globel420/Project-1/Binary_Counter_Only/Flowcharts/Binary_Counter_LED_Loop.png

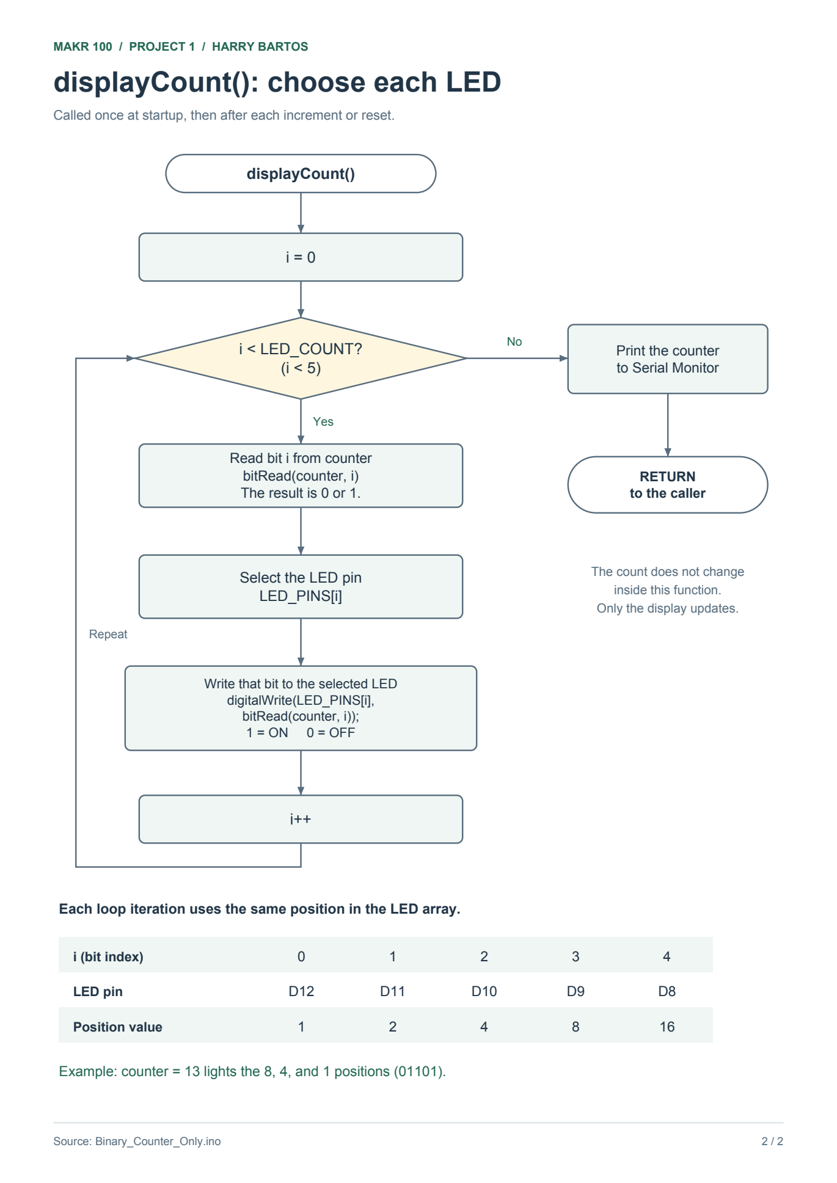
Binary_Counter_Only/Flowcharts/Binary_Counter_LED_Loop.png
