globel420/Project-1/Binary_Counter_Only/Flowcharts/Binary_Counter_Main_Flowchart.png

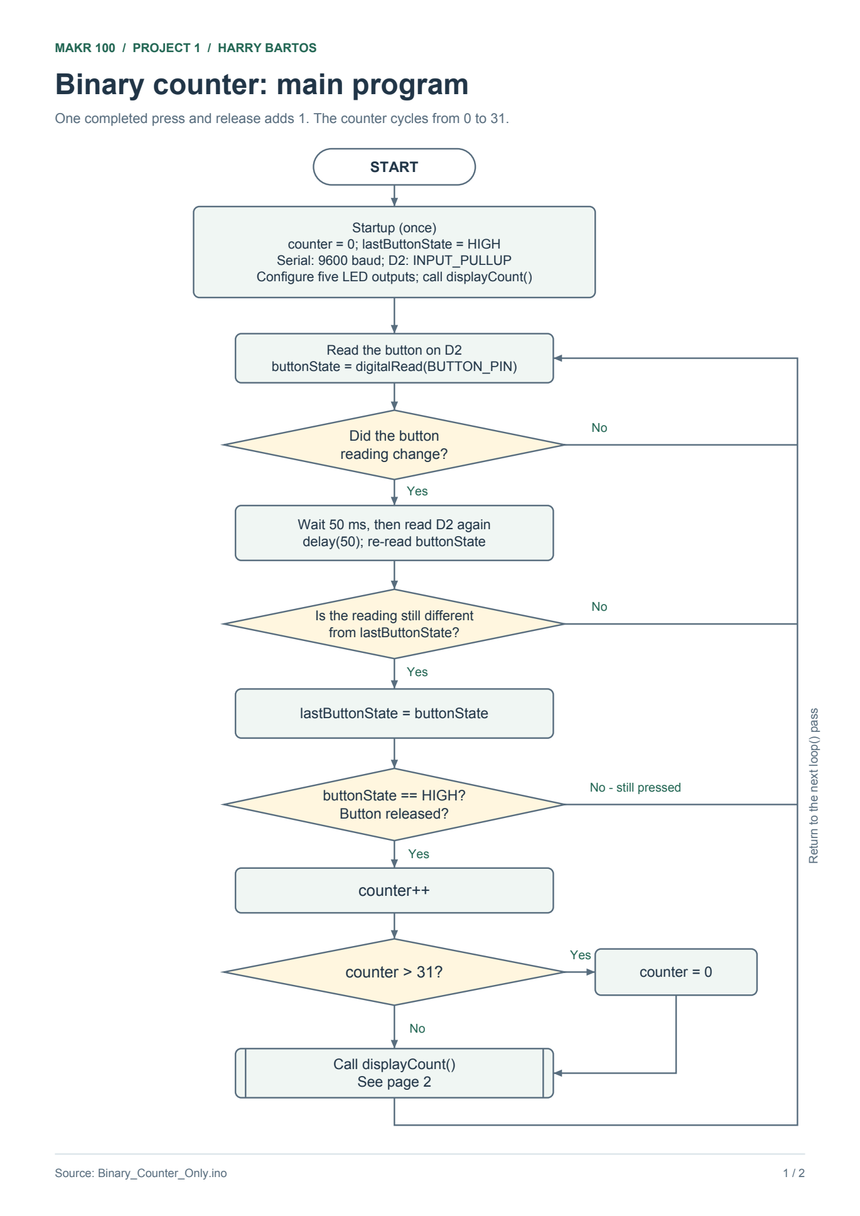
Binary_Counter_Only/Flowcharts/Binary_Counter_Main_Flowchart.png
