globel420/Project-1/Flowcharts/Program_Binary_Counter.png

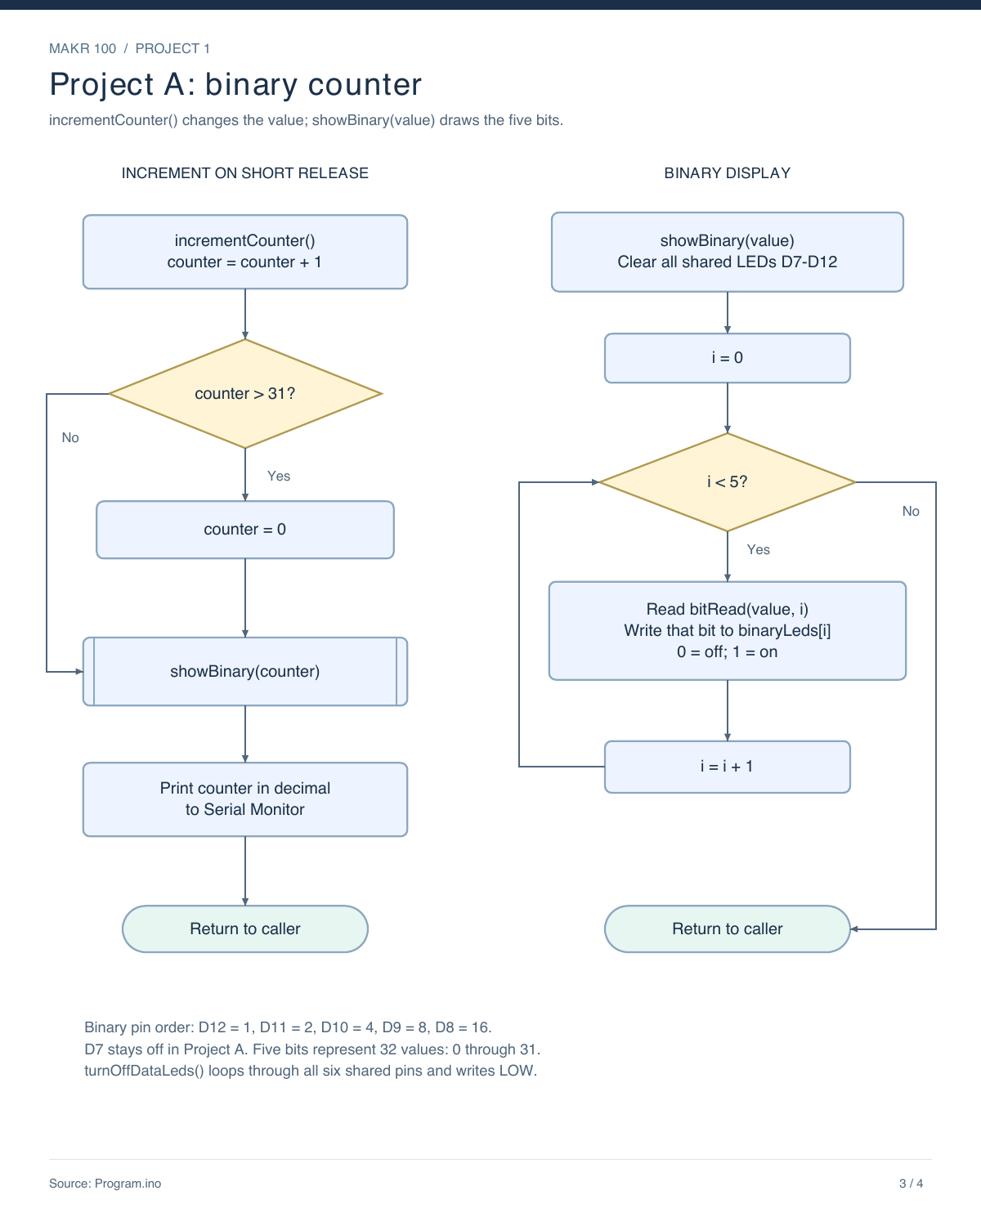
Flowcharts/Program_Binary_Counter.png
