globel420/Project-1/Flowcharts/Program_Logic_Operators.png

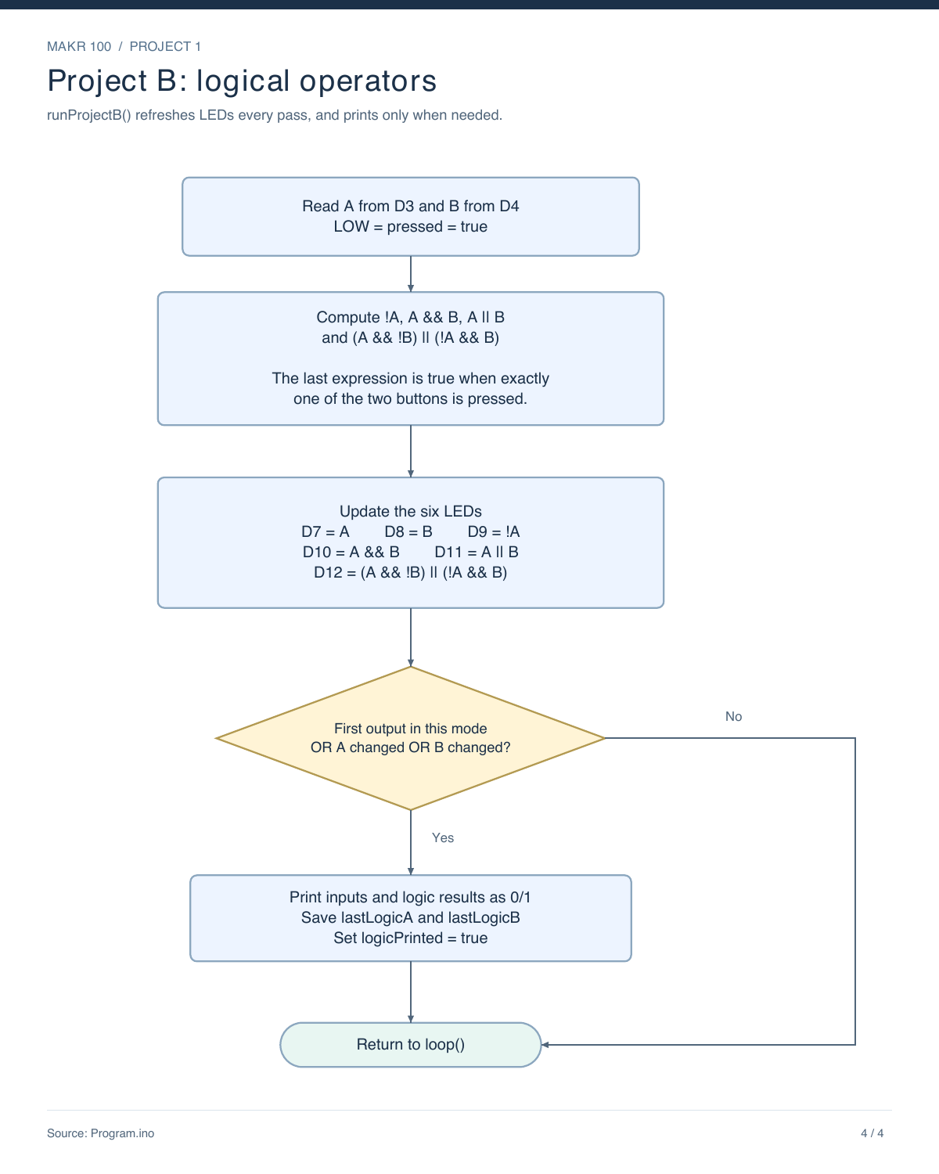
Flowcharts/Program_Logic_Operators.png
