globel420/Project-1/Flowcharts/Program_Main_Flowchart.png

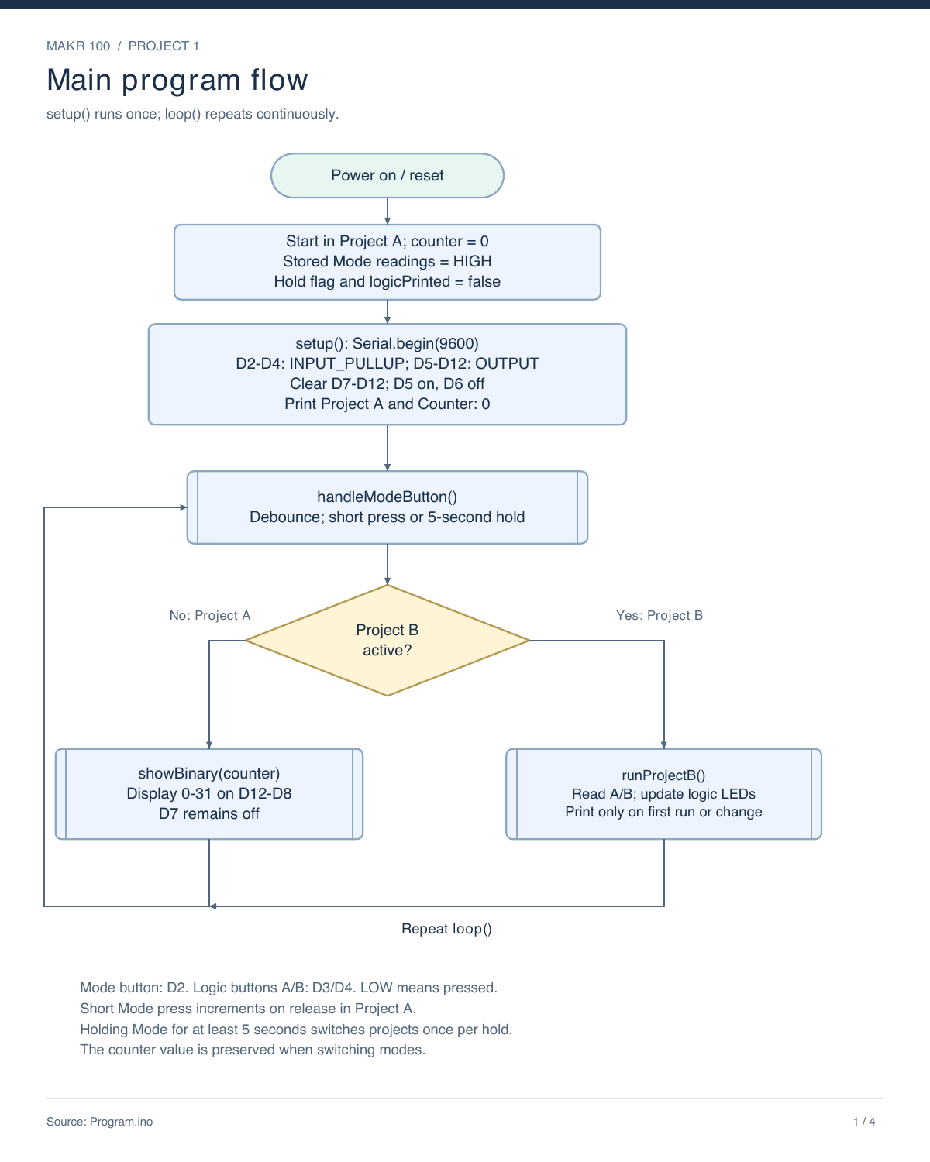
Flowcharts/Program_Main_Flowchart.png
