globel420/Project-1/Flowcharts/Program_Mode_Button.png

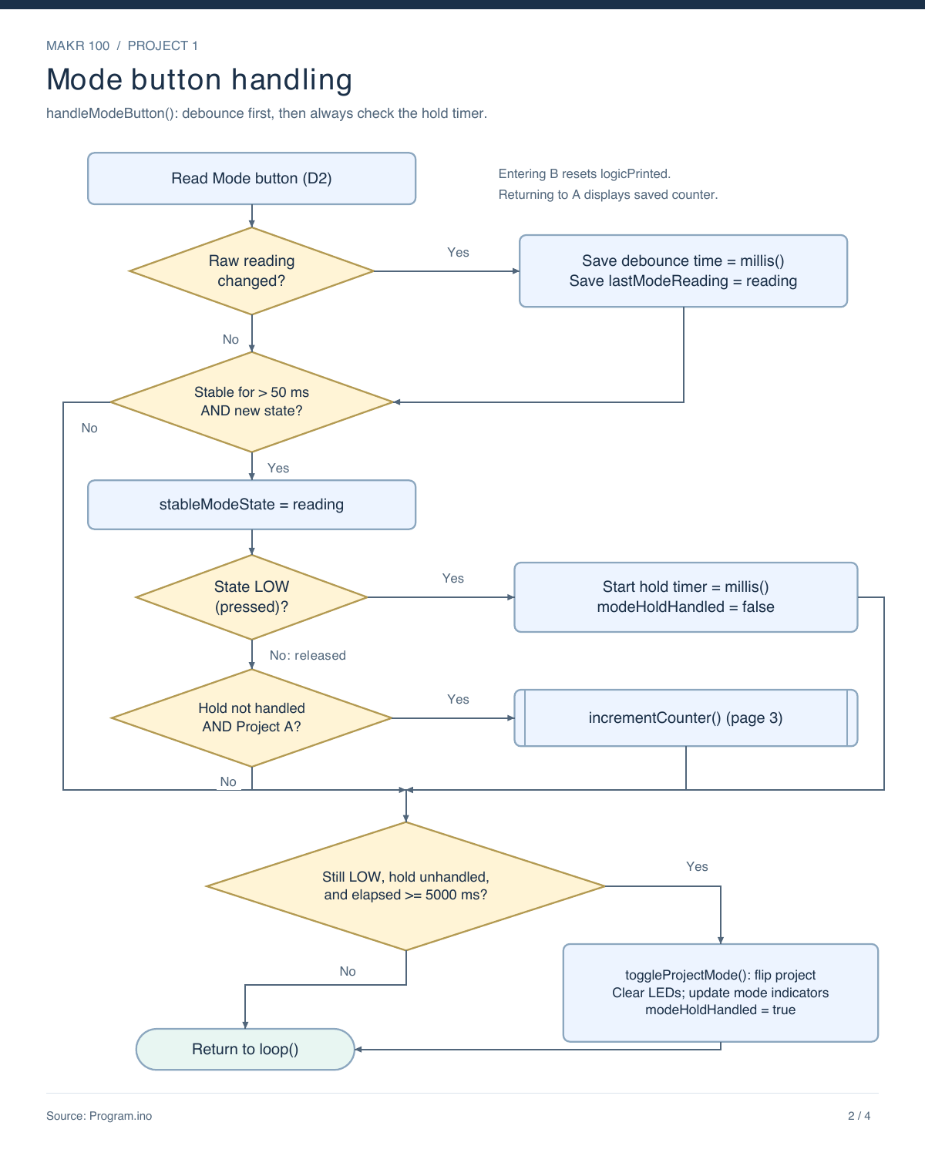
Flowcharts/Program_Mode_Button.png
