globel420/Project-1/Images/Flowchart_1_Master_Loop.png

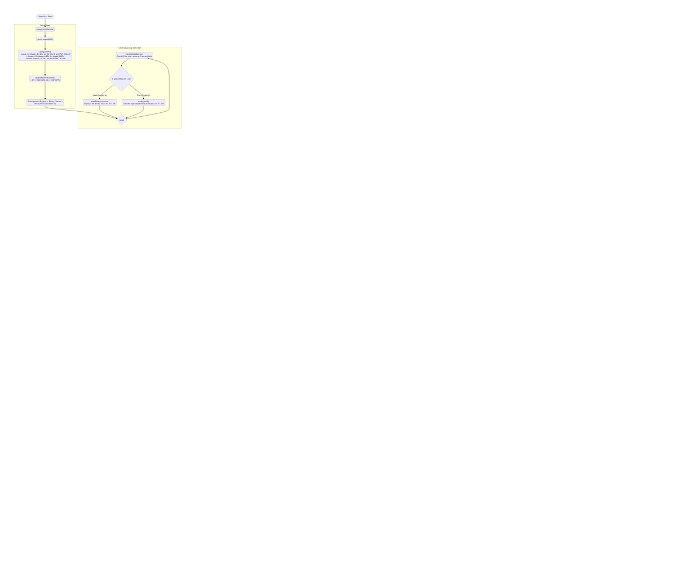
Images/Flowchart_1_Master_Loop.png
