globel420/Project-1/Images/Flowchart_2_Mode_Button.png

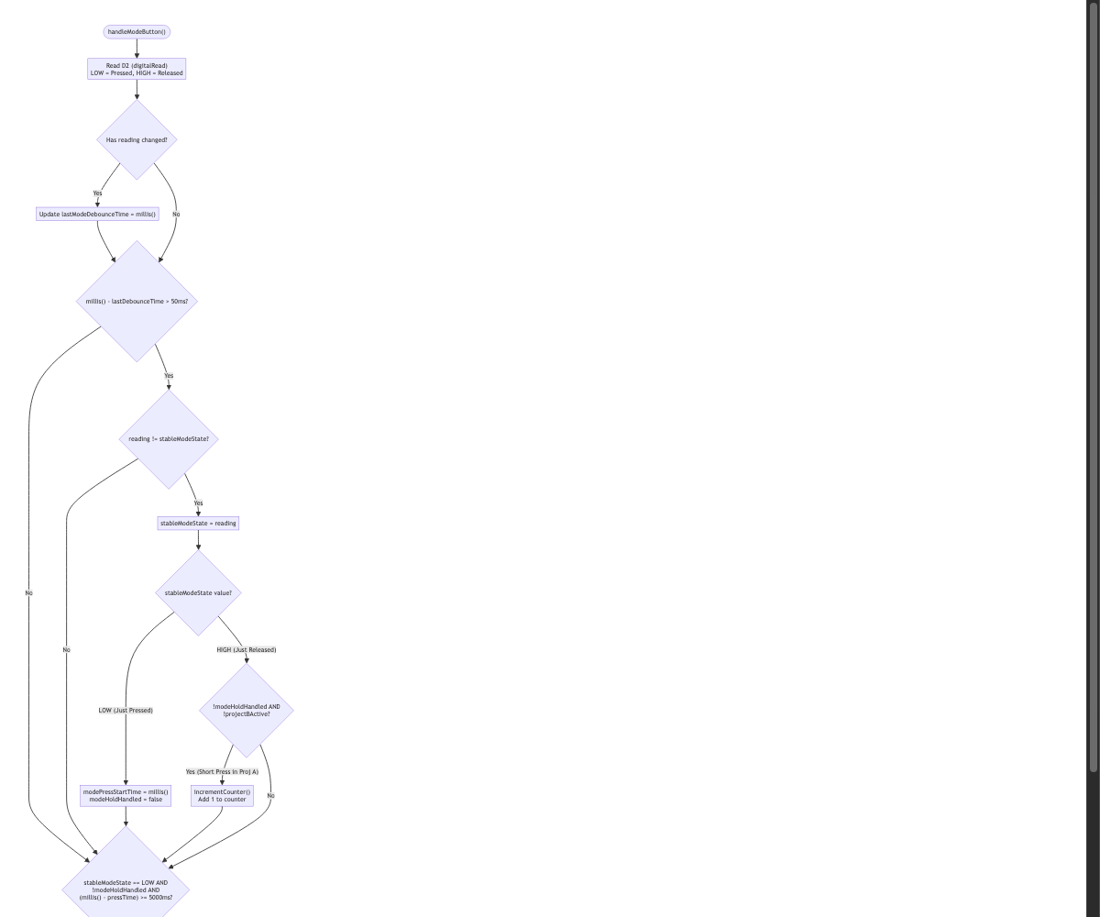
Images/Flowchart_2_Mode_Button.png
