globel420/Project-1/Images/Flowchart_4_Project_B_Logic.png

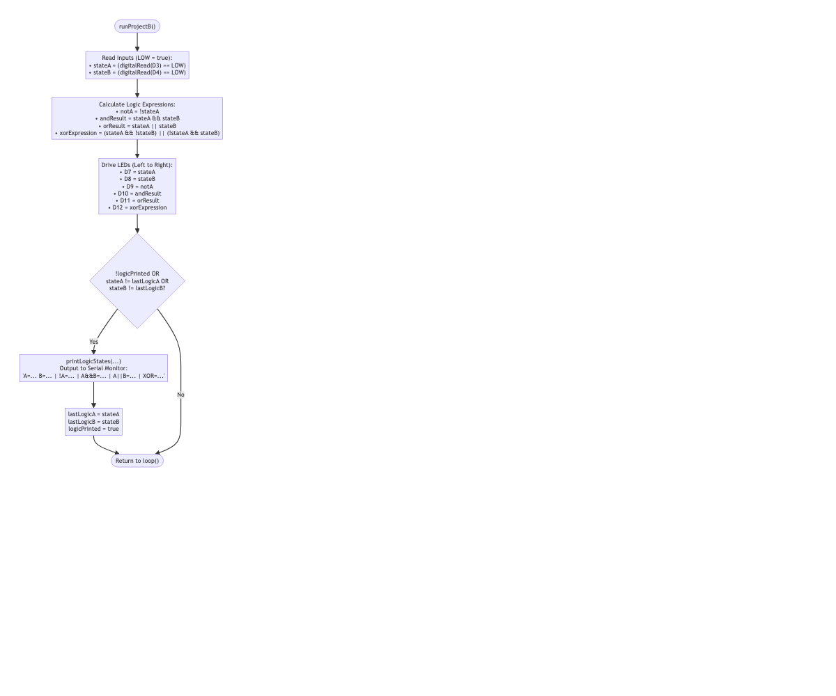
Images/Flowchart_4_Project_B_Logic.png
