globel420/Project-1/output/playwright/animation-binary-loop.png

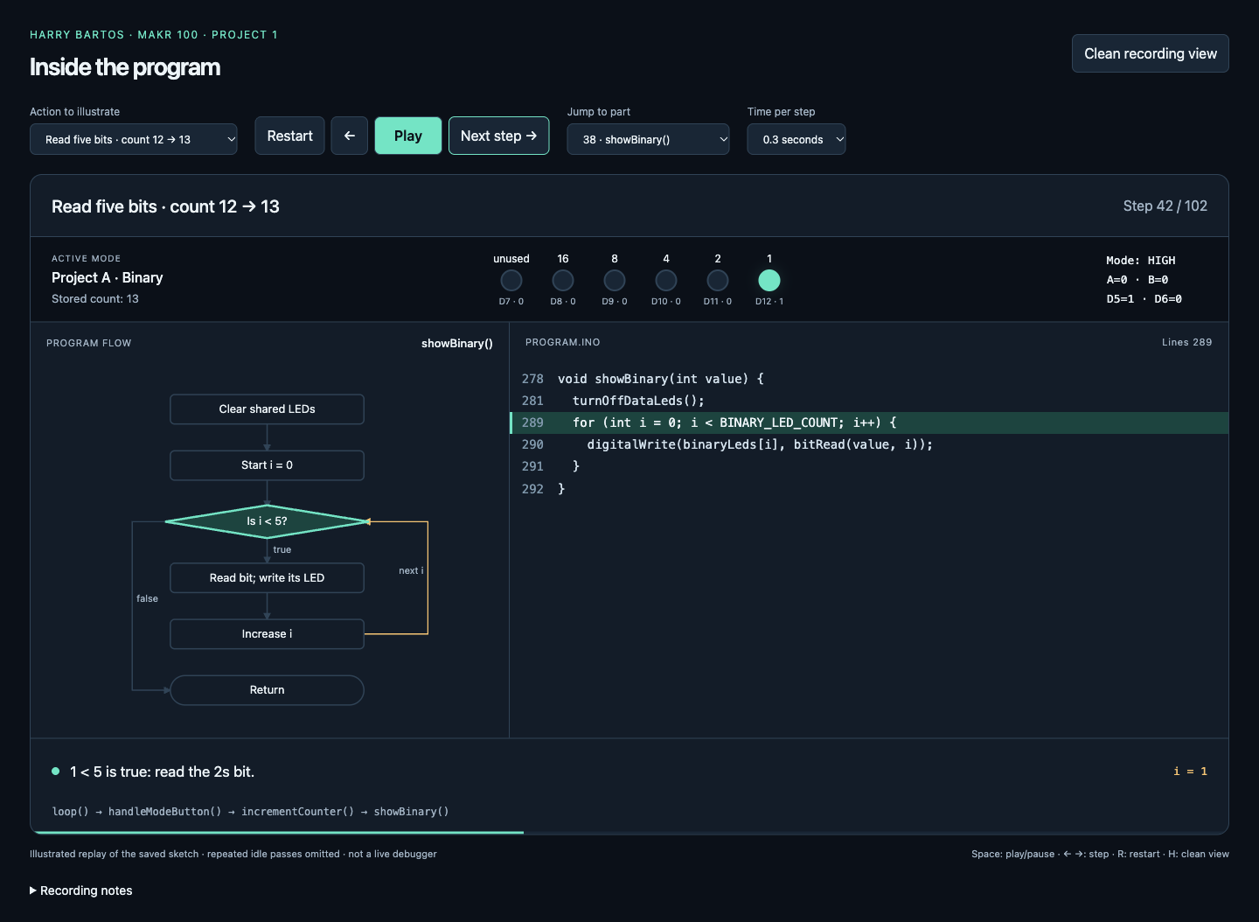
output/playwright/animation-binary-loop.png
