globel420/Project-1/output/playwright/animation-mobile.png

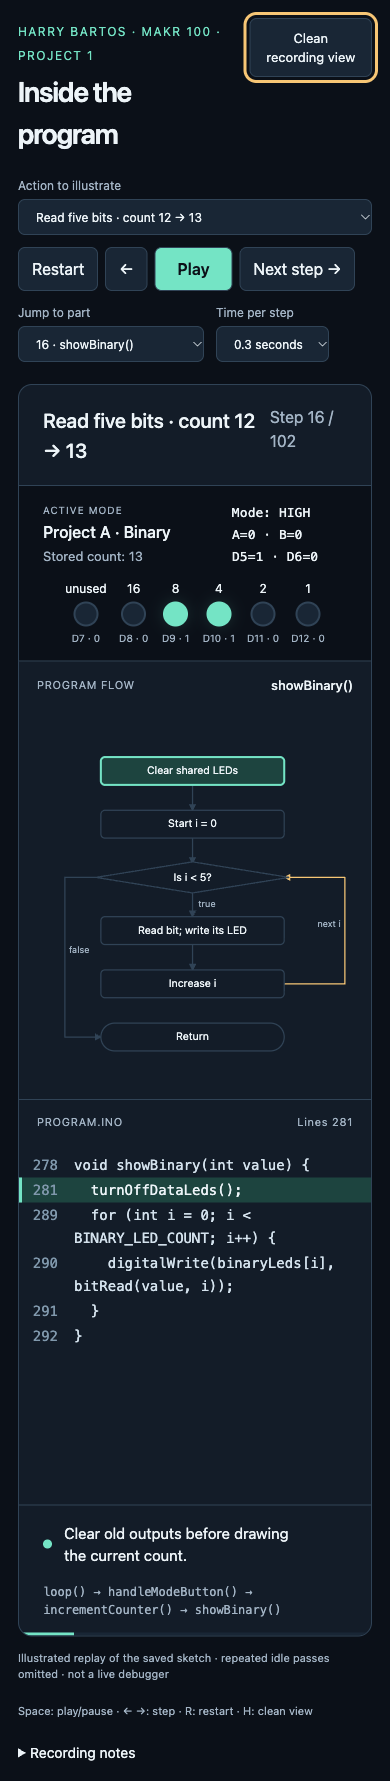
output/playwright/animation-mobile.png
