globel420/Project-1/Pictures/IMG_6296.jpeg

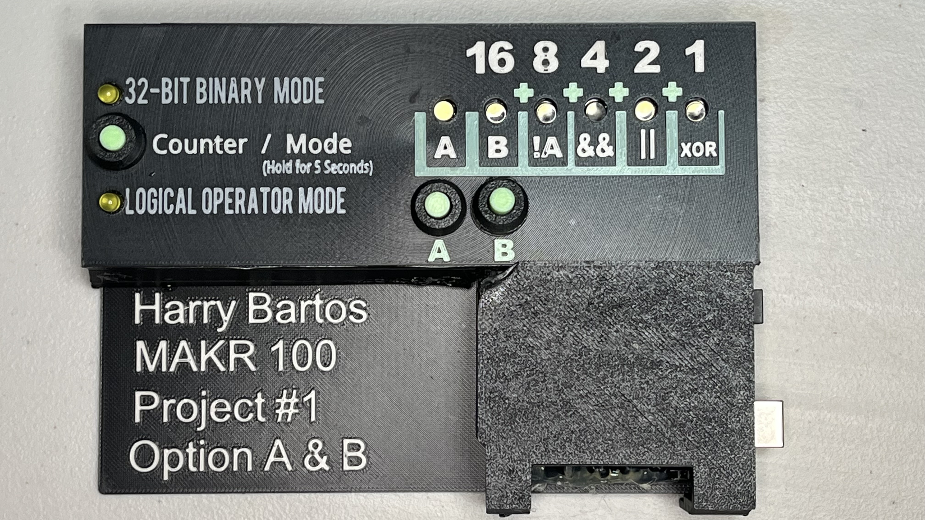
Pictures/IMG_6296.jpeg
