globel420/Project-1/Pictures/IMG_6298.jpeg

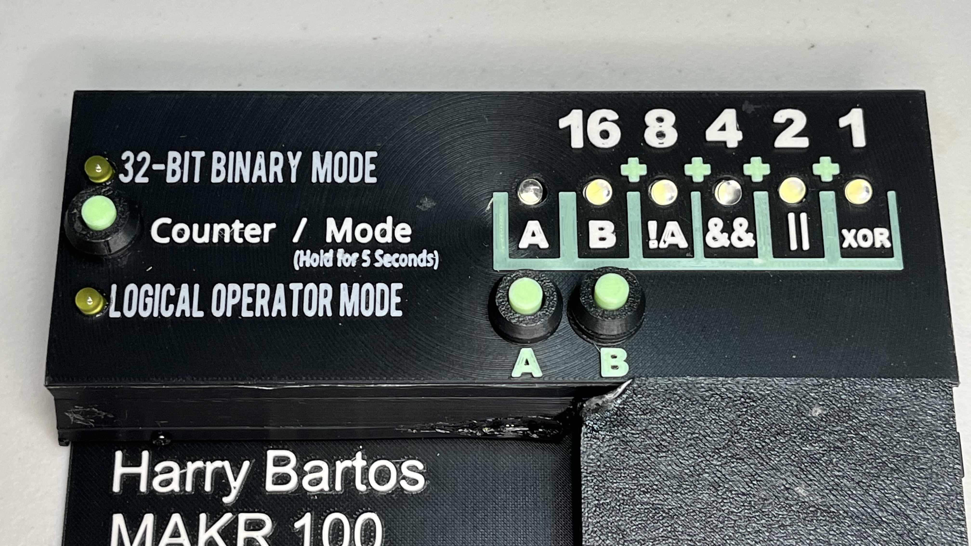
Pictures/IMG_6298.jpeg
