globel420/Project-1/Pictures/IMG_6299.jpeg

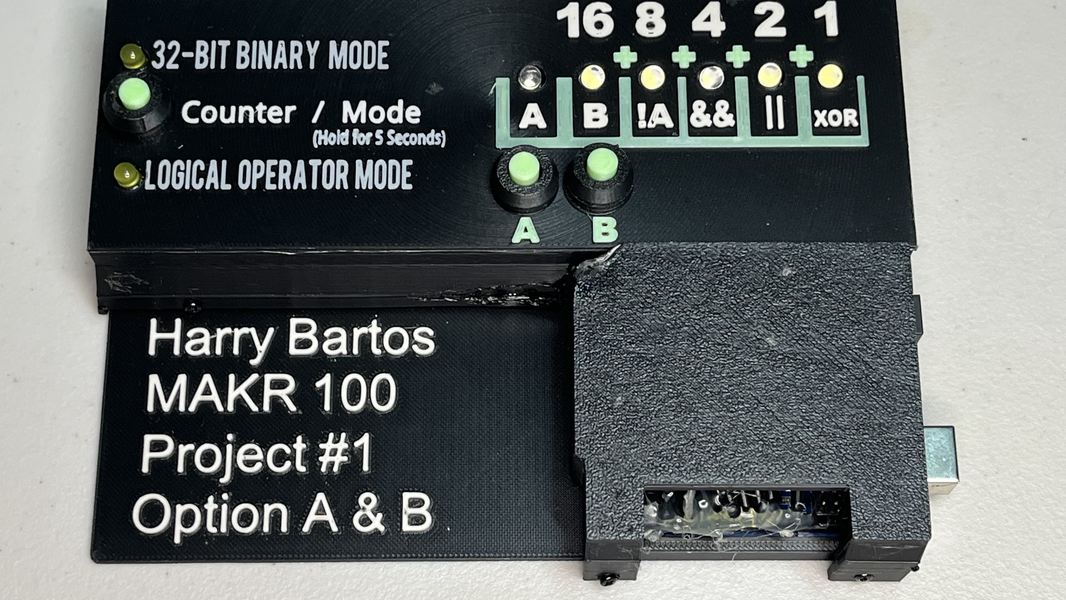
Pictures/IMG_6299.jpeg
