globel420/Project-1/Pictures/IMG_6301.jpeg

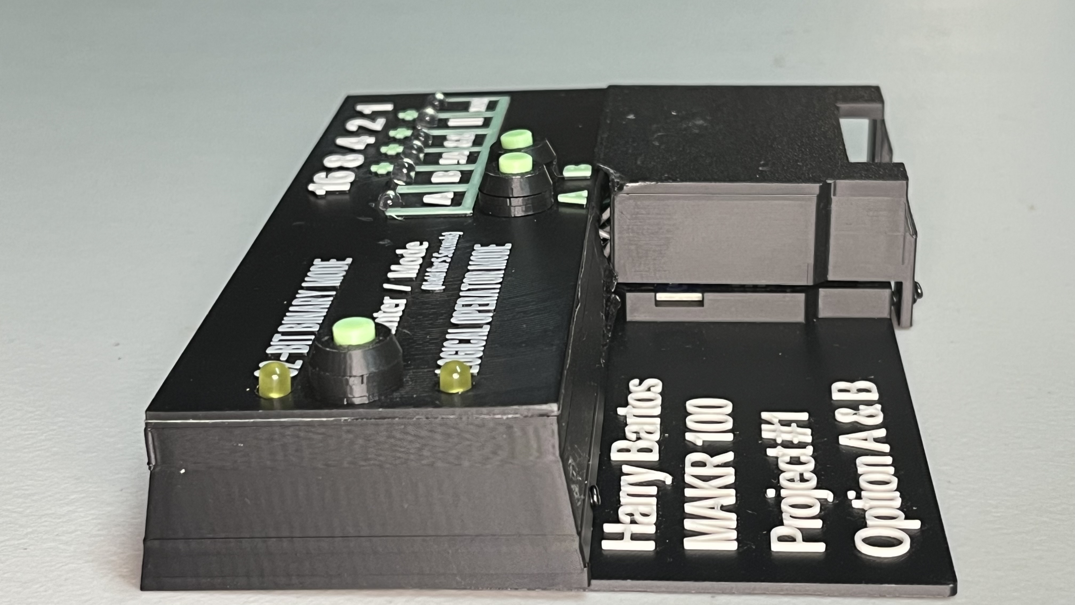
Pictures/IMG_6301.jpeg
