globel420/Project-1/Pictures/IMG_6303.jpeg

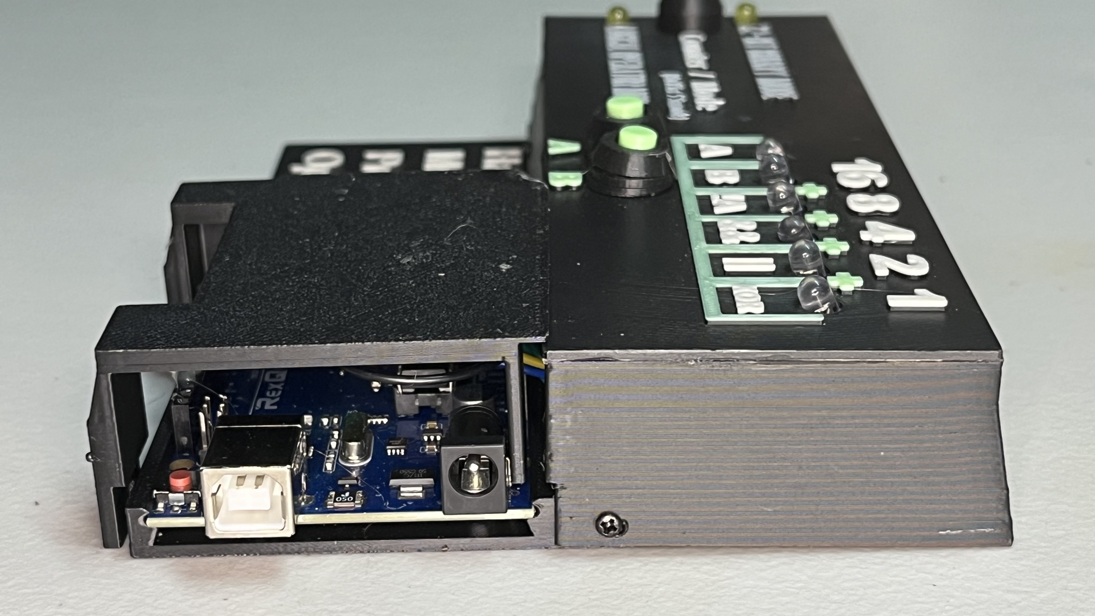
Pictures/IMG_6303.jpeg
