globel420/Project-1/Pictures/IMG_6304.jpeg

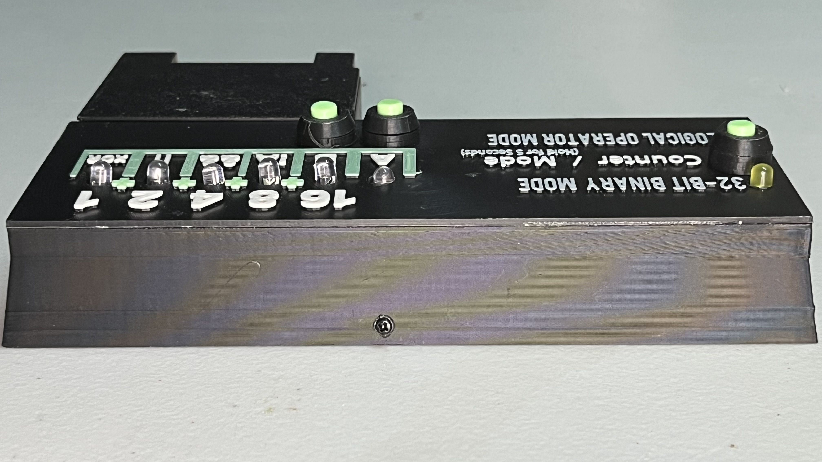
Pictures/IMG_6304.jpeg
