globel420/Project-1/Pictures/IMG_6305.jpeg

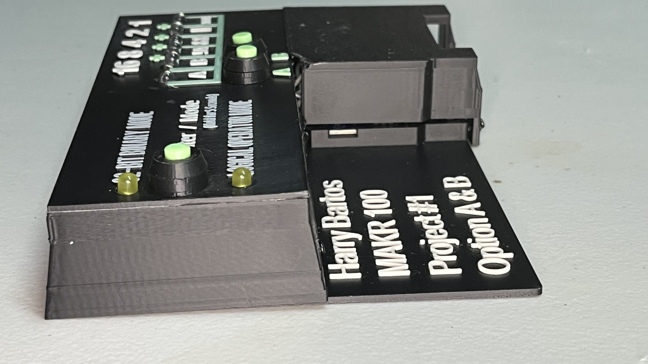
Pictures/IMG_6305.jpeg
