globel420/Project-1/Pictures/IMG_6307.jpeg

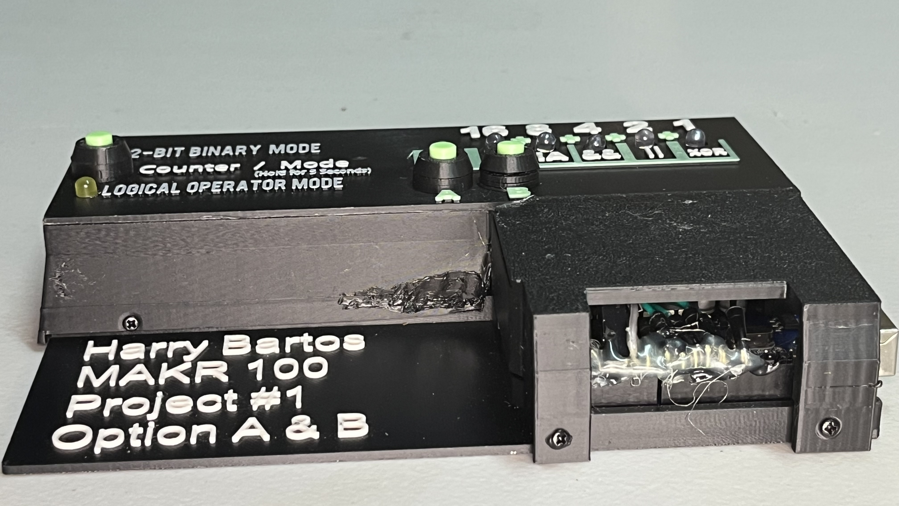
Pictures/IMG_6307.jpeg
