globel420/Project-1/Video/render_work/layout_logic.png

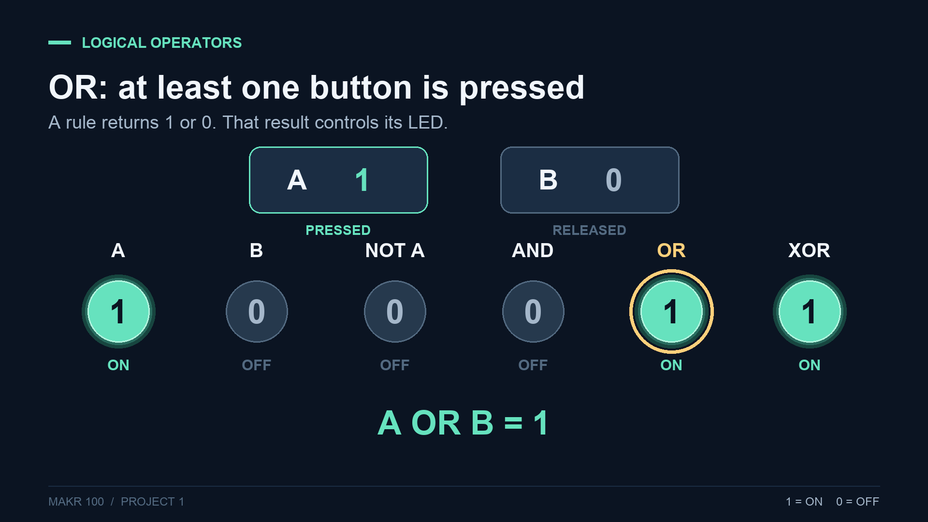
Video/render_work/layout_logic.png
