globel420/Project-1/Video/render_work/orientation_preview/07_twos_bit.png

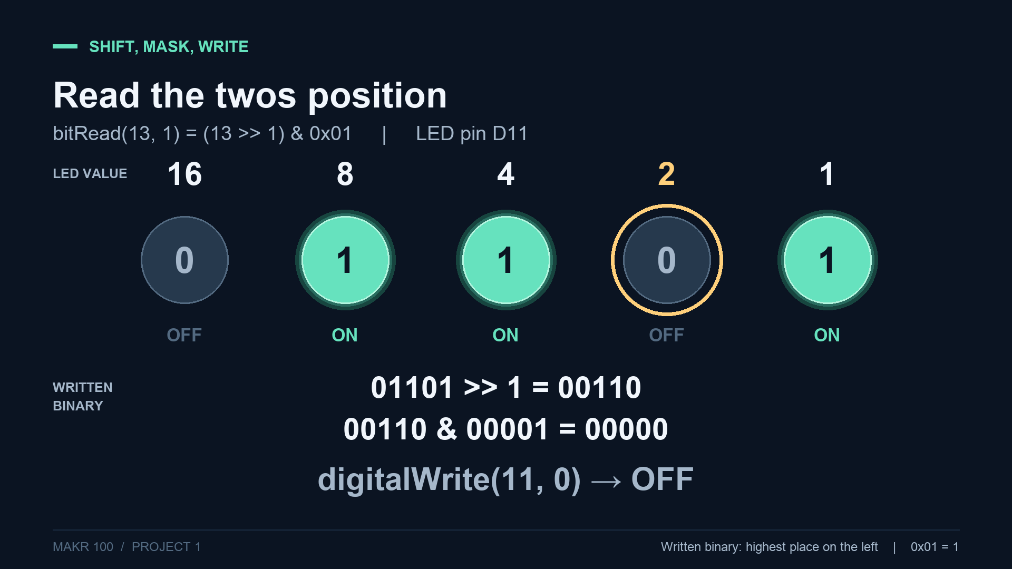
Video/render_work/orientation_preview/07_twos_bit.png
