globel420/Project-1/Video/Exports/QA_Stills/00_contact_sheet.jpg

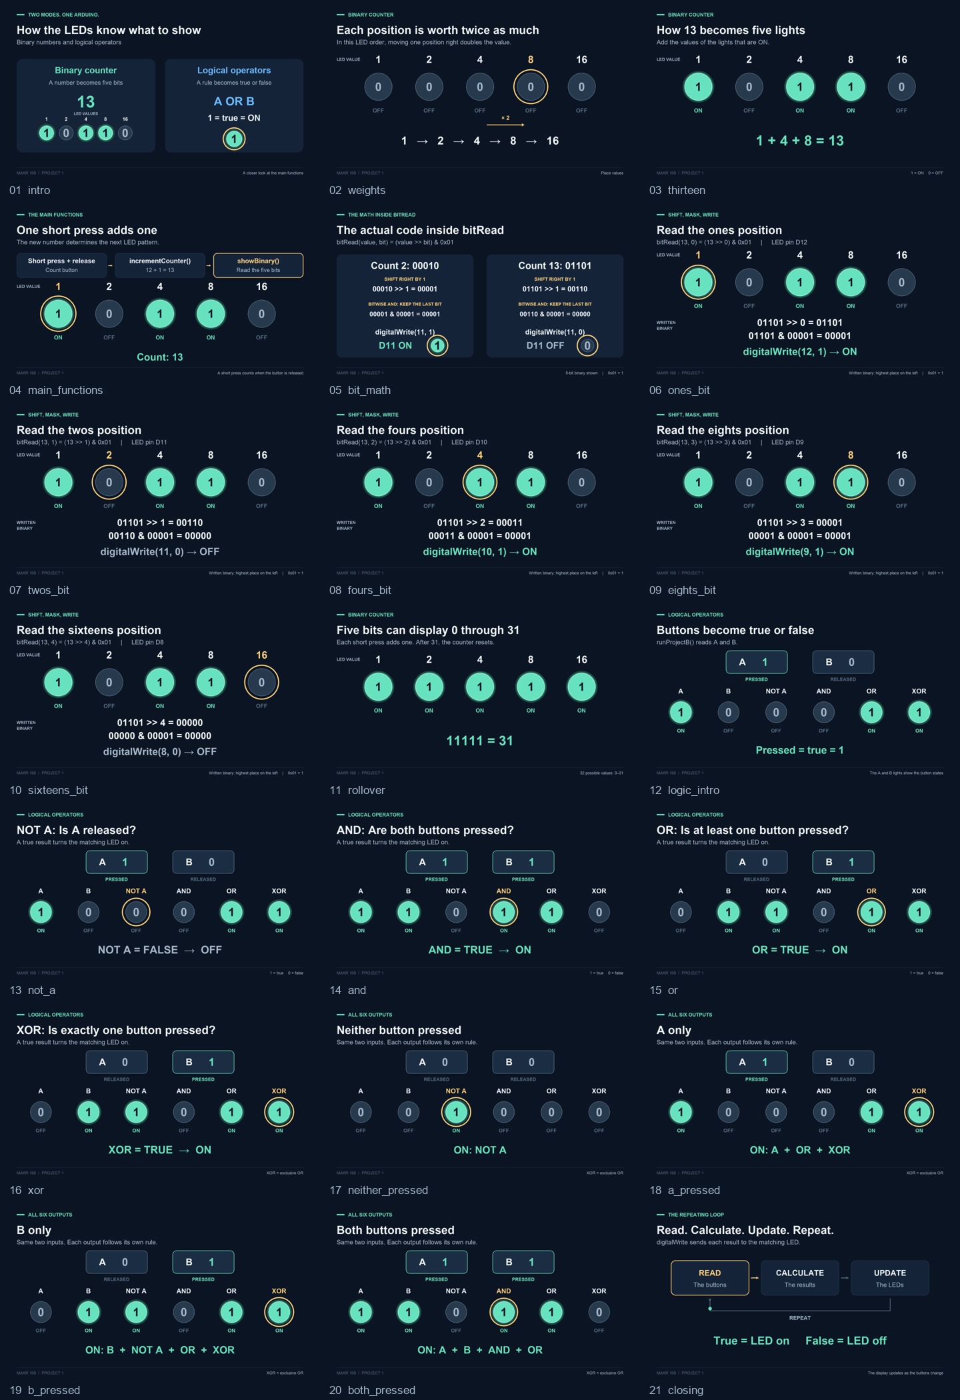
Video/Exports/QA_Stills/00_contact_sheet.jpg
