globel420/Project-1/Video/Exports/QA_Stills/01_intro.png

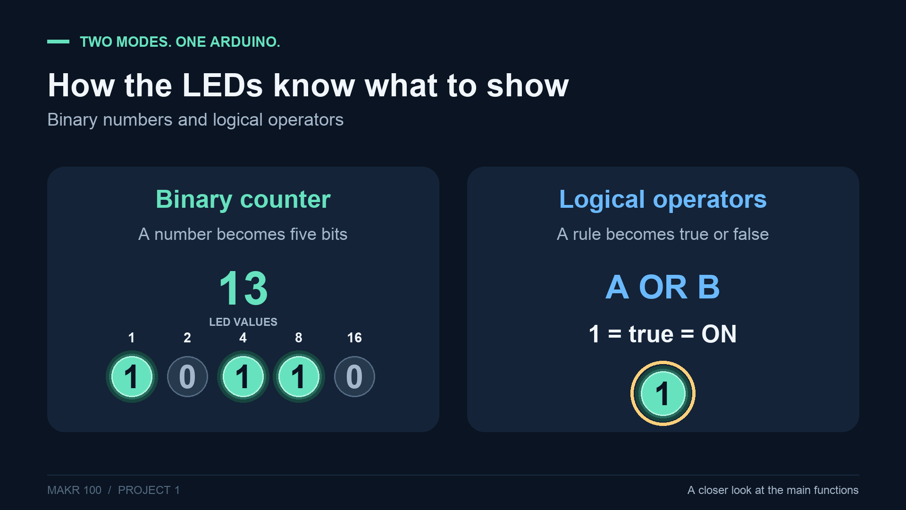
Video/Exports/QA_Stills/01_intro.png
