globel420/Project-1/Video/Exports/QA_Stills/03_thirteen.png

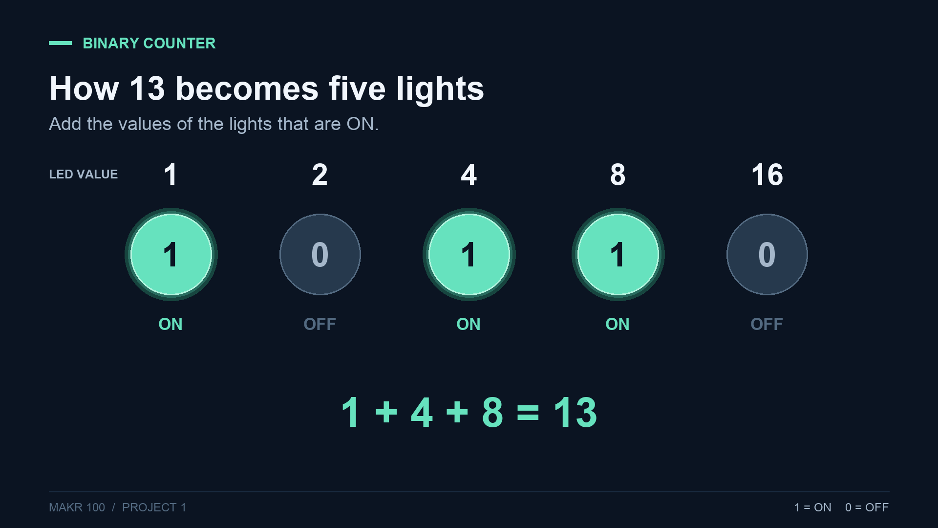
Video/Exports/QA_Stills/03_thirteen.png
