globel420/Project-1/Video/Exports/QA_Stills/04_main_functions.png

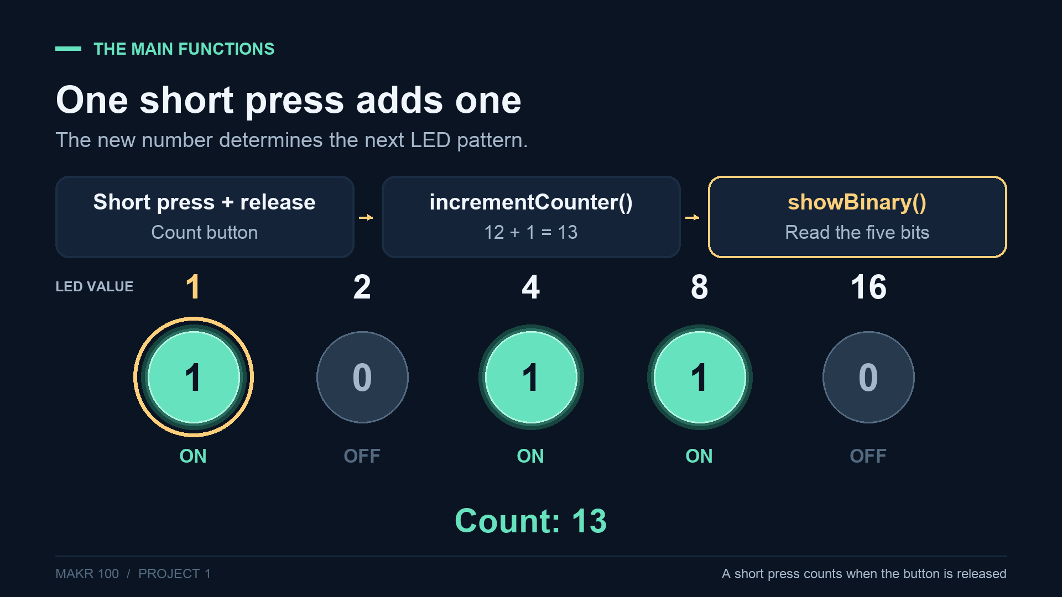
Video/Exports/QA_Stills/04_main_functions.png
