globel420/Project-1/Video/Exports/QA_Stills/05_bit_math.png

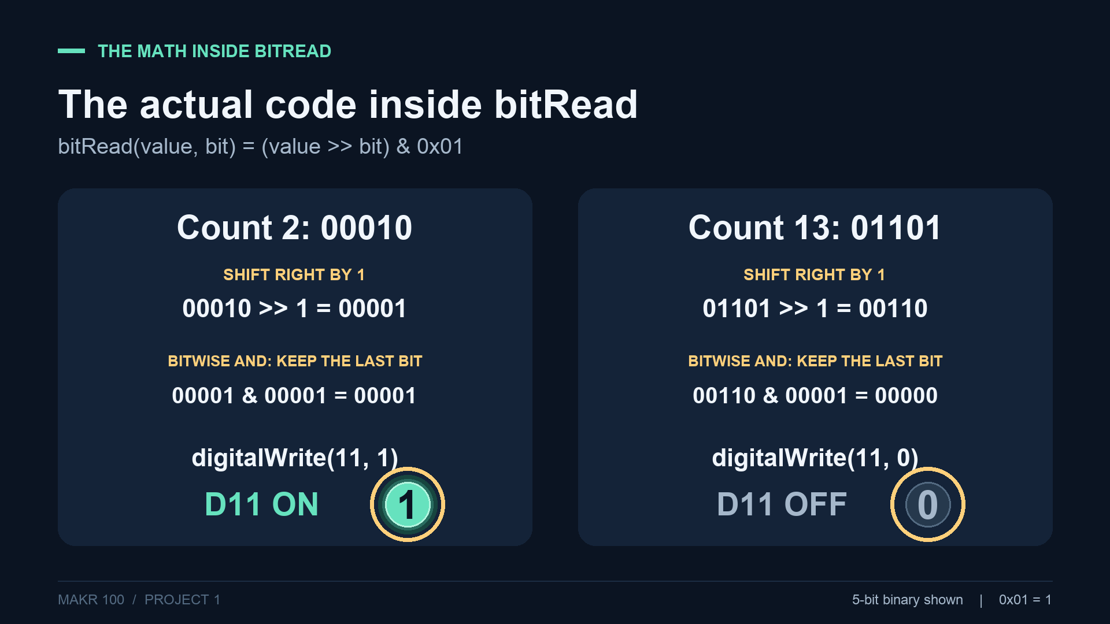
Video/Exports/QA_Stills/05_bit_math.png
