globel420/Project-1/Video/Exports/QA_Stills/06_ones_bit.png

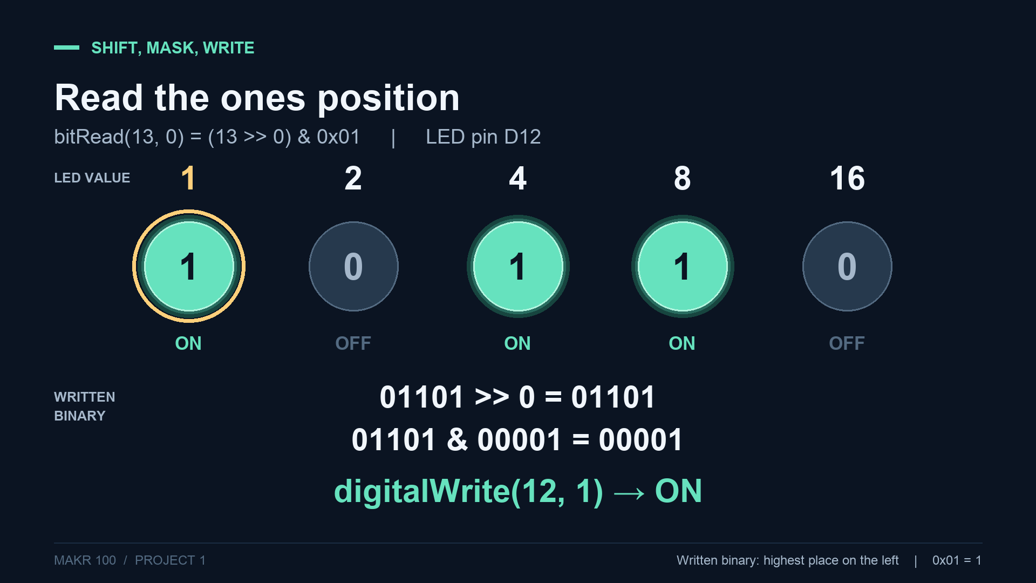
Video/Exports/QA_Stills/06_ones_bit.png
