globel420/Project-1/Video/Exports/QA_Stills/08_fours_bit.png

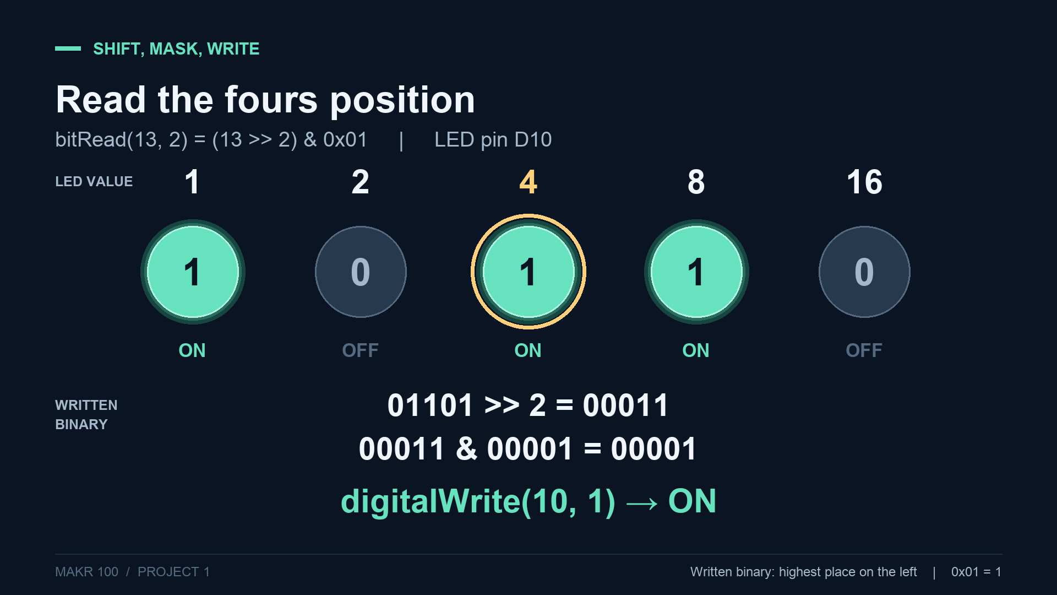
Video/Exports/QA_Stills/08_fours_bit.png
