globel420/Project-1/Video/Exports/QA_Stills/12_logic_intro.png

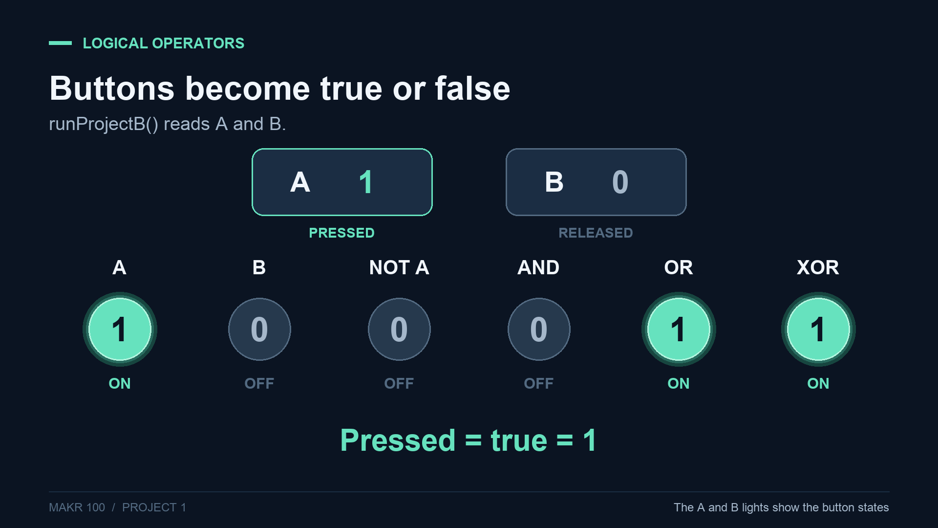
Video/Exports/QA_Stills/12_logic_intro.png
