globel420/Project-1/Video/Exports/QA_Stills/13_not_a.png

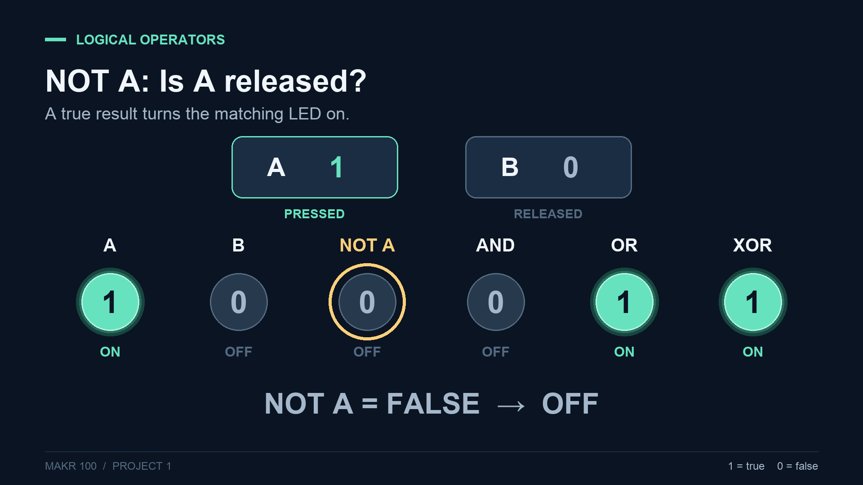
Video/Exports/QA_Stills/13_not_a.png
