globel420/Project-1/Video/Exports/QA_Stills/14_and.png

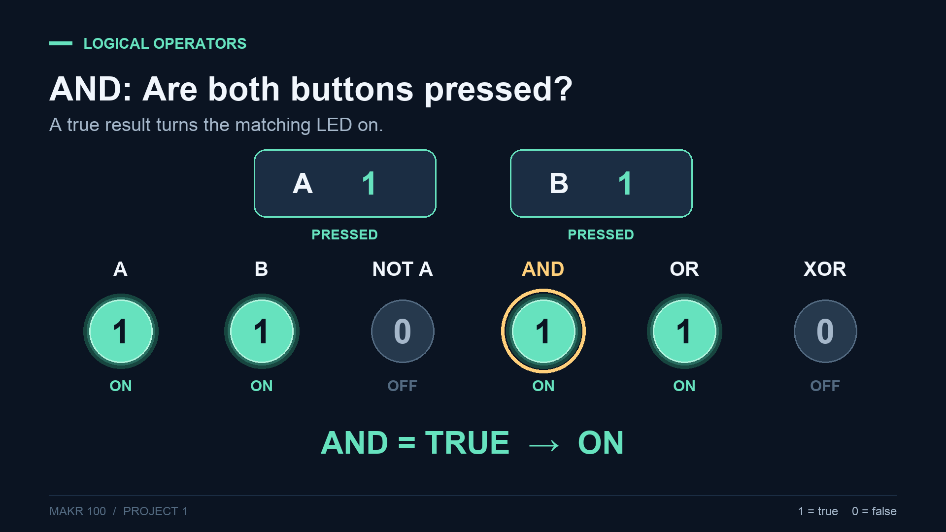
Video/Exports/QA_Stills/14_and.png
