globel420/Project-1/Video/Exports/QA_Stills/15_or.png

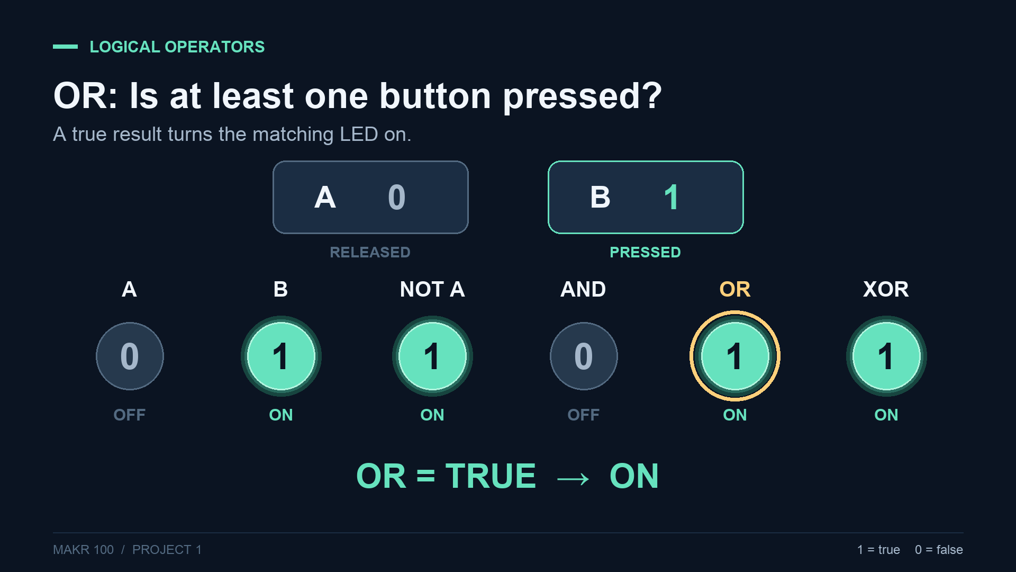
Video/Exports/QA_Stills/15_or.png
