globel420/Project-1/Video/Exports/QA_Stills/17_neither_pressed.png

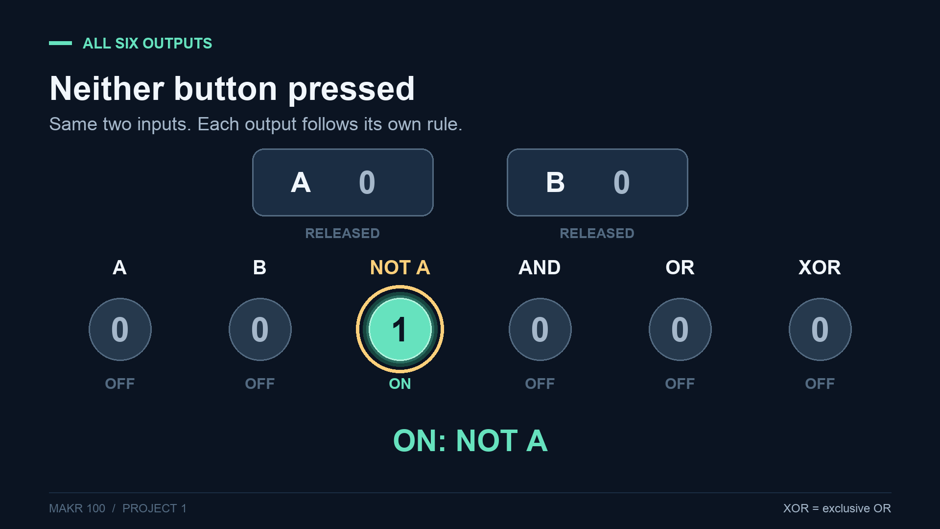
Video/Exports/QA_Stills/17_neither_pressed.png
