globel420/Project-1/Video/Exports/QA_Stills/18_a_pressed.png

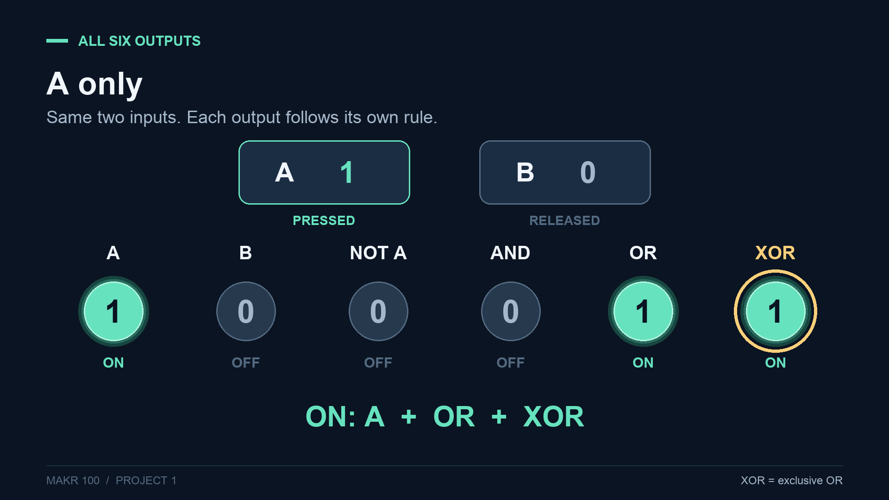
Video/Exports/QA_Stills/18_a_pressed.png
