globel420/Project-1/Video/Exports/QA_Stills/19_b_pressed.png

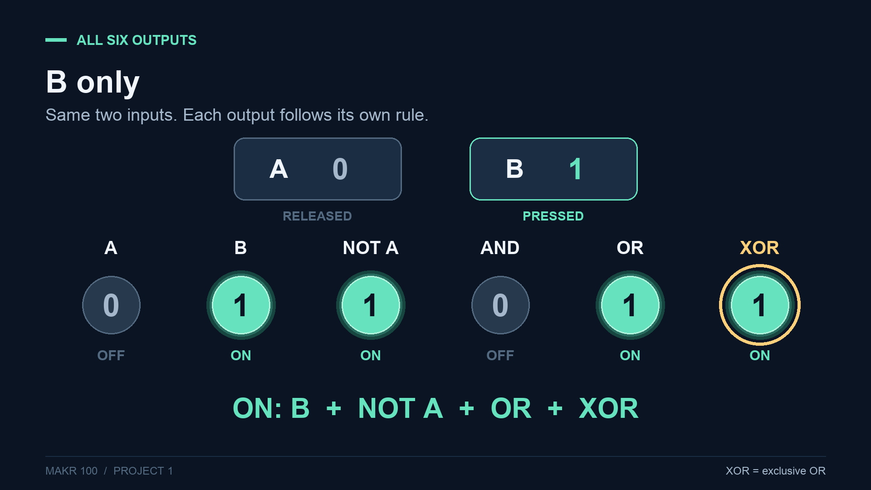
Video/Exports/QA_Stills/19_b_pressed.png
