globel420/Project-1/Video/Exports/QA_Stills/21_closing.png

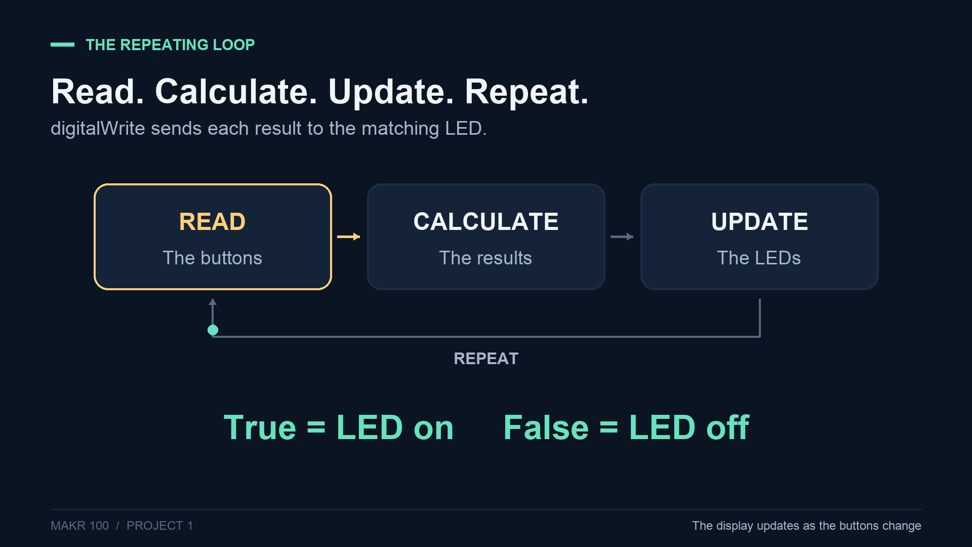
Video/Exports/QA_Stills/21_closing.png
