globel420/Project-1/Video/Exports/QA_Stills/23_counter_incremented_before_led_update.png

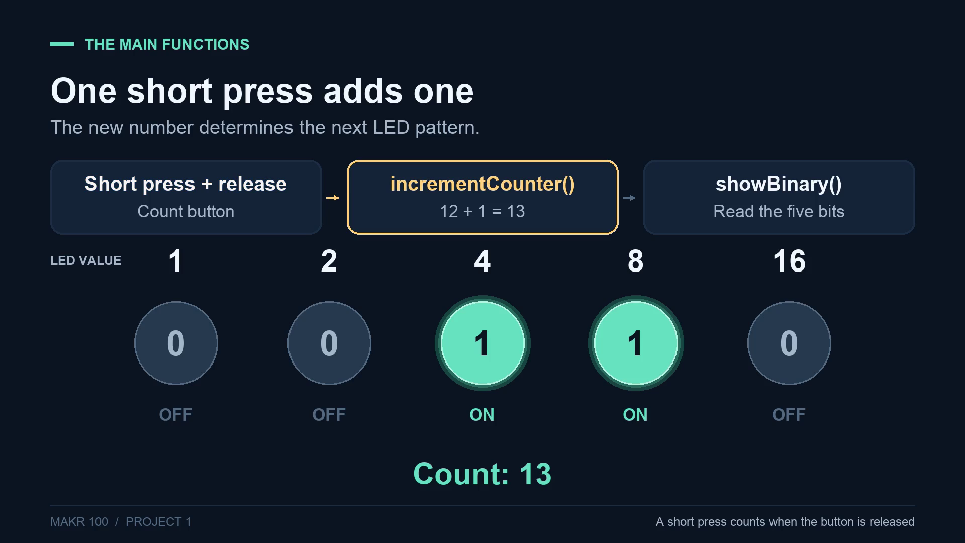
Video/Exports/QA_Stills/23_counter_incremented_before_led_update.png
