globel420/Project-1/Video/QA/code-example.png

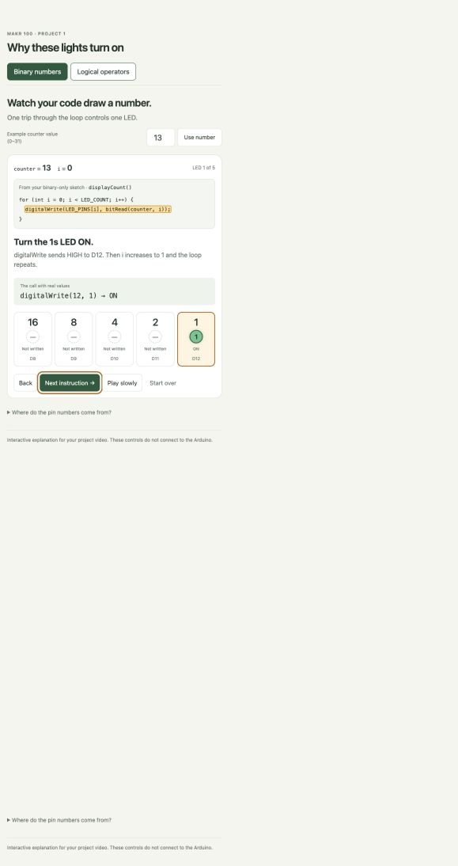
Video/QA/code-example.png
